Nordln/FoneyCase-Phone-case-for-Samsung-S23/all_shot.JPG

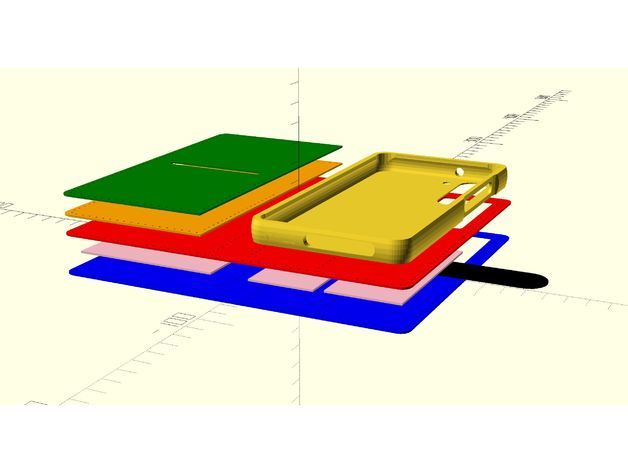
all_shot.JPG
