Nordln/FoneyCase-Phone-case-for-Samsung-S23/card_wallet_1mm.png

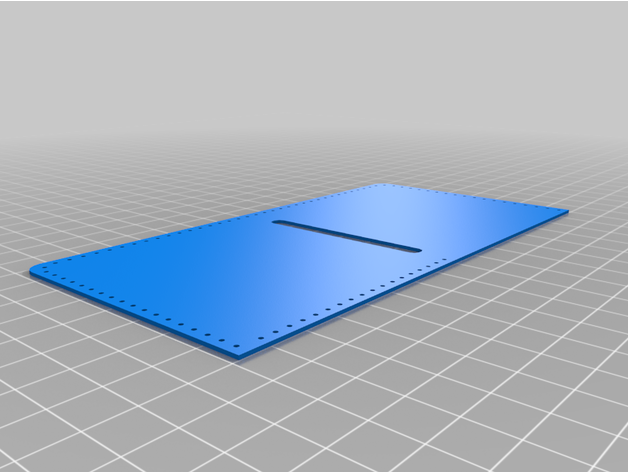
card_wallet_1mm.png
