Nordln/FoneyCase-Phone-case-for-Samsung-S23/holder_1mm.png

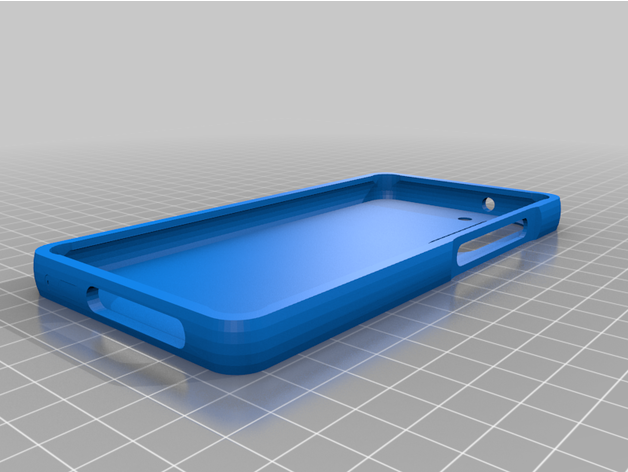
holder_1mm.png
