Nordln/FoneyCase-Phone-case-for-Samsung-S23/plates_1mm.png

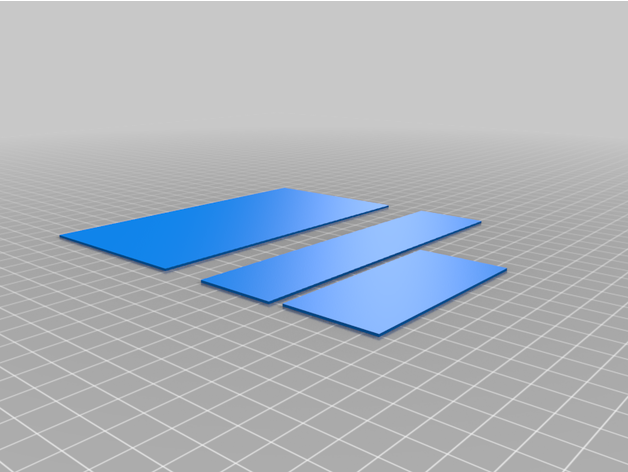
plates_1mm.png
